osptek/esp32-s3-touch-lcd-4/versions/ESP32-S3-Touch-4-Classic/docs/ESP32-S3-Touch基础板V1.0.pdf

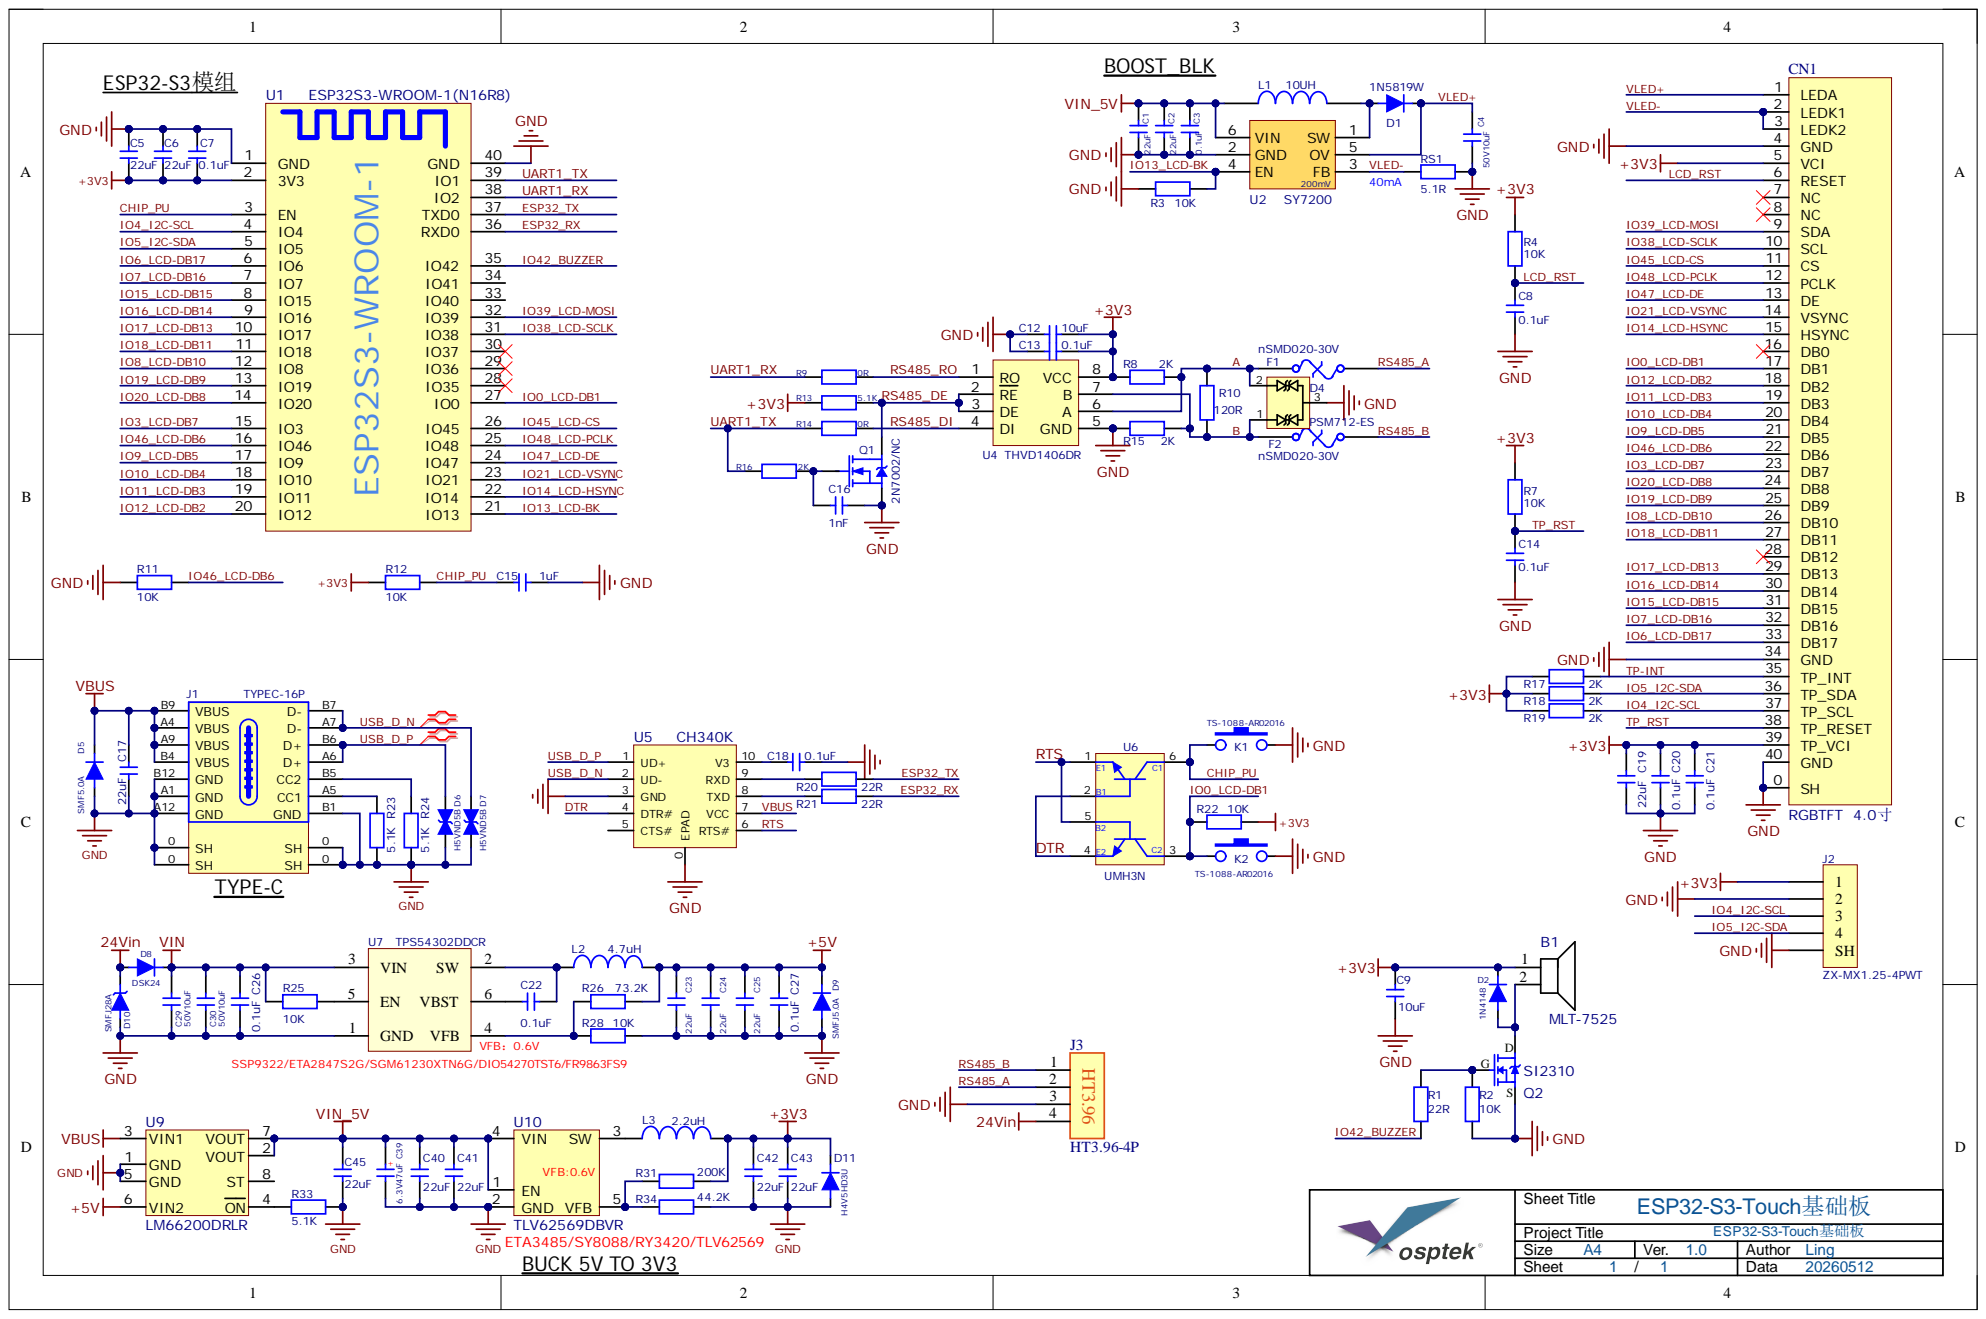
[picture p32: page 1]

C5 | C6 | C7
22uF | 22uF | 0.1uF | 3V3 2 GND 1

Size A4 | Ver. 1.0 | Author Ling
Sheet 1 / 1 | | Data 20260512
