osptek/esp32-s3-touch-lcd-4/versions/ESP32-S3-Touch-4-Pro/docs/ESP32-S3-Touch-Pro_V1.1.pdf

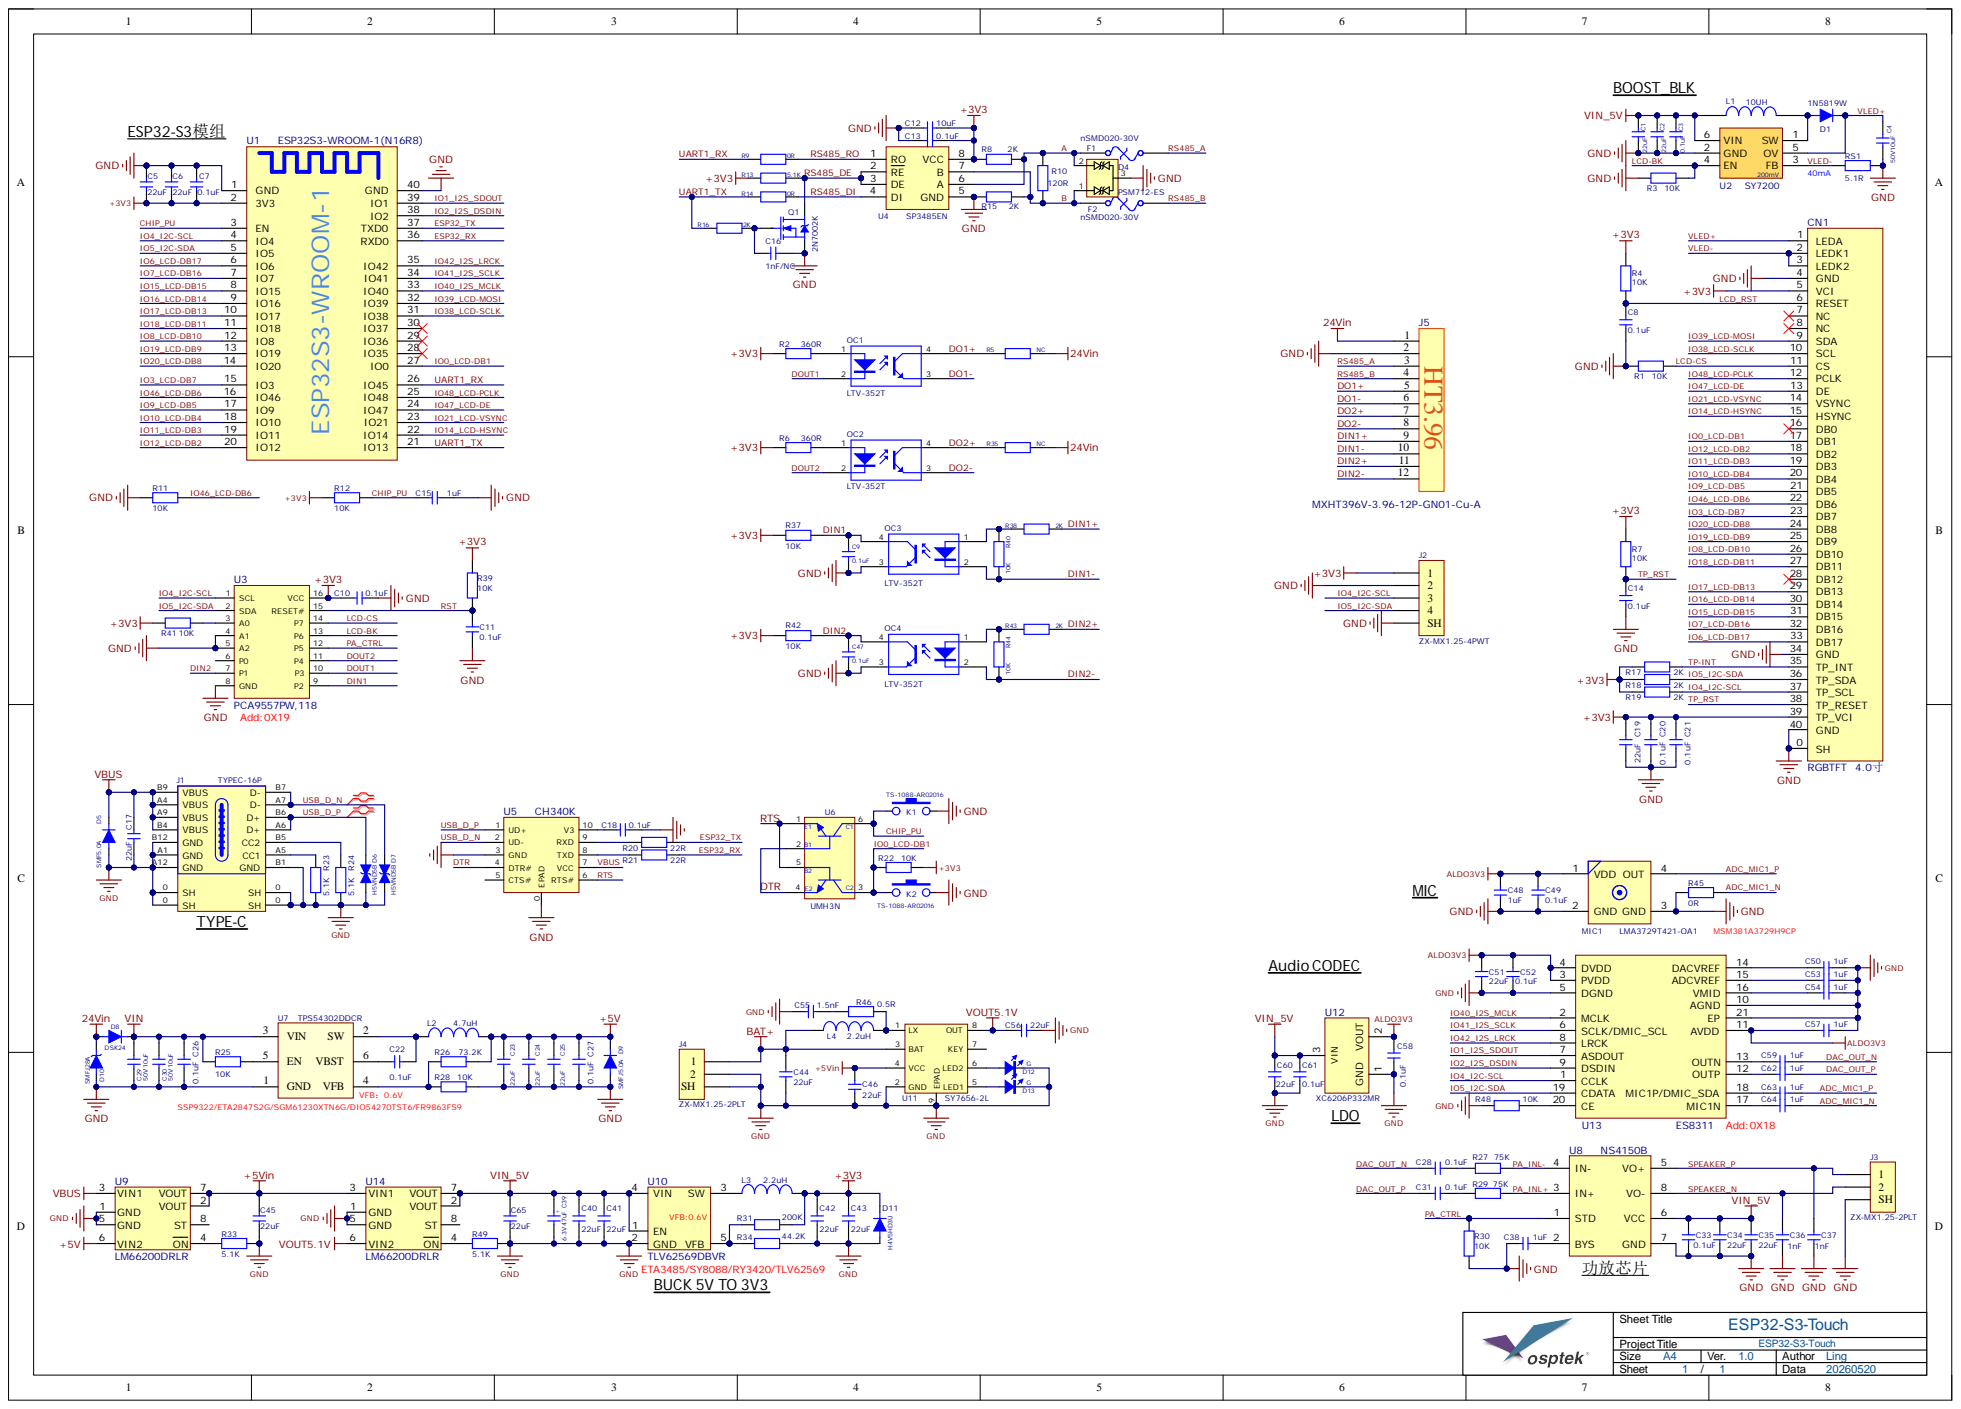
[picture p35: page 1]

R17 | 2K IO5_I2C-SDA | TP_SDA 36
R18 | 2K IO4_I2C-SCL | TP_SCL 37

Size A4 | Ver. 1.0 | Author Ling
Sheet 1 / 1 | | Data 20260520
