osptek/esp32-s3-touch-lcd-4/versions/ESP32-S3-Touch-4-Pro/examples/esp32-s3-touch-lcd-4-pro-demo/main/lvgl_port.c

/*
 * SPDX-FileCopyrightText: 2023-2024 Espressif Systems (Shanghai) CO LTD
 *
 * SPDX-License-Identifier: Apache-2.0
 */

#include "freertos/FreeRTOS.h"
#include "freertos/semphr.h"
#include "freertos/task.h"
#include "esp_lcd_panel_ops.h"
#include "esp_lcd_panel_rgb.h"
#include "esp_lcd_touch.h"
#include "esp_timer.h"
#include "esp_log.h"
#include "lvgl.h"
#include "lvgl_port.h"

static const char *TAG = "lv_port";
static SemaphoreHandle_t lvgl_mux; // LVGL 互斥锁
static TaskHandle_t lvgl_task_handle = NULL;

static void flush_callback(lv_display_t *disp, const lv_area_t *area, uint8_t *px_map)
{
    esp_lcd_panel_handle_t panel_handle = (esp_lcd_panel_handle_t)lv_display_get_user_data(disp);
    const int offsetx1 = area->x1;
    const int offsetx2 = area->x2;
    const int offsety1 = area->y1;
    const int offsety2 = area->y2;

    if (lv_display_flush_is_last(disp))
    {
        esp_lcd_panel_draw_bitmap(panel_handle, offsetx1, offsety1, offsetx2 + 1, offsety2 + 1, px_map);

        ulTaskNotifyValueClear(NULL, ULONG_MAX);
        ulTaskNotifyTake(pdTRUE, portMAX_DELAY);
    }

    lv_display_flush_ready(disp);
}

static lv_display_t *display_init(esp_lcd_panel_handle_t panel_handle)
{
    assert(panel_handle);

    ESP_LOGD(TAG, "使用 RGB 面板双帧缓冲作为 LVGL 绘图缓冲");

    void *buf1 = NULL;
    void *buf2 = NULL;
    const int buffer_size = LVGL_PORT_H_RES * LVGL_PORT_V_RES;
    ESP_ERROR_CHECK(esp_lcd_rgb_panel_get_frame_buffer(panel_handle, 2, &buf1, &buf2));

    lv_display_t *disp = lv_display_create(LVGL_PORT_H_RES, LVGL_PORT_V_RES);
    if (!disp)
    {
        ESP_LOGE(TAG, "创建显示设备失败");
        return NULL;
    }

    lv_display_set_buffers(disp, buf1, buf2, buffer_size * sizeof(lv_color_t), LV_DISPLAY_RENDER_MODE_PARTIAL);
    lv_display_set_flush_cb(disp, flush_callback);
    lv_display_set_user_data(disp, panel_handle);
    lv_display_set_render_mode(disp, LV_DISPLAY_RENDER_MODE_DIRECT);

    return disp;
}

static void touchpad_read(lv_indev_t *indev, lv_indev_data_t *data)
{
    static uint16_t last_x;
    static uint16_t last_y;
    static uint8_t missed_frames;
    static bool touch_down;

    esp_lcd_touch_handle_t tp = (esp_lcd_touch_handle_t)lv_indev_get_user_data(indev);
    assert(tp);

    uint16_t touchpad_x;
    uint16_t touchpad_y;
    uint8_t touchpad_cnt = 0;

    esp_lcd_touch_read_data(tp);

    bool touchpad_pressed = esp_lcd_touch_get_coordinates(tp, &touchpad_x, &touchpad_y, NULL, &touchpad_cnt, 1);
    if (touchpad_pressed && touchpad_cnt > 0)
    {
        last_x = touchpad_x;
        last_y = touchpad_y;
        missed_frames = 0;
        touch_down = true;
        data->point.x = touchpad_x;
        data->point.y = touchpad_y;
        data->state = LV_INDEV_STATE_PRESSED;
        ESP_LOGD(TAG, "触摸位置: %d,%d", touchpad_x, touchpad_y);
    }
    else if (touch_down && missed_frames < 2)
    {
        /* FT6336U 偶尔可能漏报单帧；短暂保持按下状态，避免拖动被打断。 */
        missed_frames++;
        data->point.x = last_x;
        data->point.y = last_y;
        data->state = LV_INDEV_STATE_PRESSED;
    }
    else
    {
        missed_frames = 0;
        touch_down = false;
        data->state = LV_INDEV_STATE_RELEASED;
    }
}

static lv_indev_t *indev_init(esp_lcd_touch_handle_t tp)
{
    assert(tp);

    lv_indev_t *indev = lv_indev_create();
    if (!indev)
    {
        ESP_LOGE(TAG, "创建输入设备失败");
        return NULL;
    }

    lv_indev_set_type(indev, LV_INDEV_TYPE_POINTER);
    lv_indev_set_read_cb(indev, touchpad_read);
    lv_indev_set_user_data(indev, tp);

    return indev;
}

static void tick_increment(void *arg)
{
    lv_tick_inc(LVGL_PORT_TICK_PERIOD_MS);
}

static esp_err_t tick_init(void)
{
    const esp_timer_create_args_t lvgl_tick_timer_args = {
        .callback = &tick_increment,
        .name = "LVGL tick"};
    esp_timer_handle_t lvgl_tick_timer = NULL;
    ESP_ERROR_CHECK(esp_timer_create(&lvgl_tick_timer_args, &lvgl_tick_timer));
    return esp_timer_start_periodic(lvgl_tick_timer, LVGL_PORT_TICK_PERIOD_MS * 1000);
}

static void lvgl_port_task(void *arg)
{
    ESP_LOGD(TAG, "启动 LVGL 任务");

    uint32_t task_delay_ms = LVGL_PORT_TASK_MAX_DELAY_MS;
    while (1)
    {
        if (lvgl_port_lock(0))
        {
            task_delay_ms = lv_timer_handler();
            lvgl_port_unlock();
        }
        if (task_delay_ms > LVGL_PORT_TASK_MAX_DELAY_MS)
        {
            task_delay_ms = LVGL_PORT_TASK_MAX_DELAY_MS;
        }
        else if (task_delay_ms < LVGL_PORT_TASK_MIN_DELAY_MS)
        {
            task_delay_ms = LVGL_PORT_TASK_MIN_DELAY_MS;
        }
        vTaskDelay(pdMS_TO_TICKS(task_delay_ms));
    }
}

esp_err_t lvgl_port_init(esp_lcd_panel_handle_t lcd_handle, esp_lcd_touch_handle_t tp_handle)
{
    lv_init();
    ESP_ERROR_CHECK(tick_init());

    lv_display_t *disp = display_init(lcd_handle);
    assert(disp);

    if (tp_handle)
    {
        lv_indev_t *indev = indev_init(tp_handle);
        assert(indev);
    }

    lvgl_mux = xSemaphoreCreateRecursiveMutex();
    assert(lvgl_mux);

    ESP_LOGI(TAG, "创建 LVGL 任务");
    BaseType_t core_id = (LVGL_PORT_TASK_CORE < 0) ? tskNO_AFFINITY : LVGL_PORT_TASK_CORE;
    BaseType_t ret = xTaskCreatePinnedToCore(lvgl_port_task, "lvgl", LVGL_PORT_TASK_STACK_SIZE, NULL,
                                             LVGL_PORT_TASK_PRIORITY, &lvgl_task_handle, core_id);
    if (ret != pdPASS)
    {
        ESP_LOGE(TAG, "创建 LVGL 任务失败");
        return ESP_FAIL;
    }

    return ESP_OK;
}

bool lvgl_port_lock(int timeout_ms)
{
    assert(lvgl_mux && "必须先调用 lvgl_port_init");

    const TickType_t timeout_ticks = (timeout_ms < 0) ? portMAX_DELAY : pdMS_TO_TICKS(timeout_ms);
    return xSemaphoreTakeRecursive(lvgl_mux, timeout_ticks) == pdTRUE;
}

void lvgl_port_unlock(void)
{
    assert(lvgl_mux && "必须先调用 lvgl_port_init");
    xSemaphoreGiveRecursive(lvgl_mux);
}

bool lvgl_port_notify_rgb_vsync(void)
{
    BaseType_t need_yield = pdFALSE;
    xTaskNotifyFromISR(lvgl_task_handle, ULONG_MAX, eNoAction, &need_yield);
    return (need_yield == pdTRUE);
}
